DaveBerkeley/mains-power-control/kicad/mains-power-control/mains-power-control.kicad_sch

## KiCad design kicad/mains-power-control/mains-power-control.kicad_sch (2026-01-26)

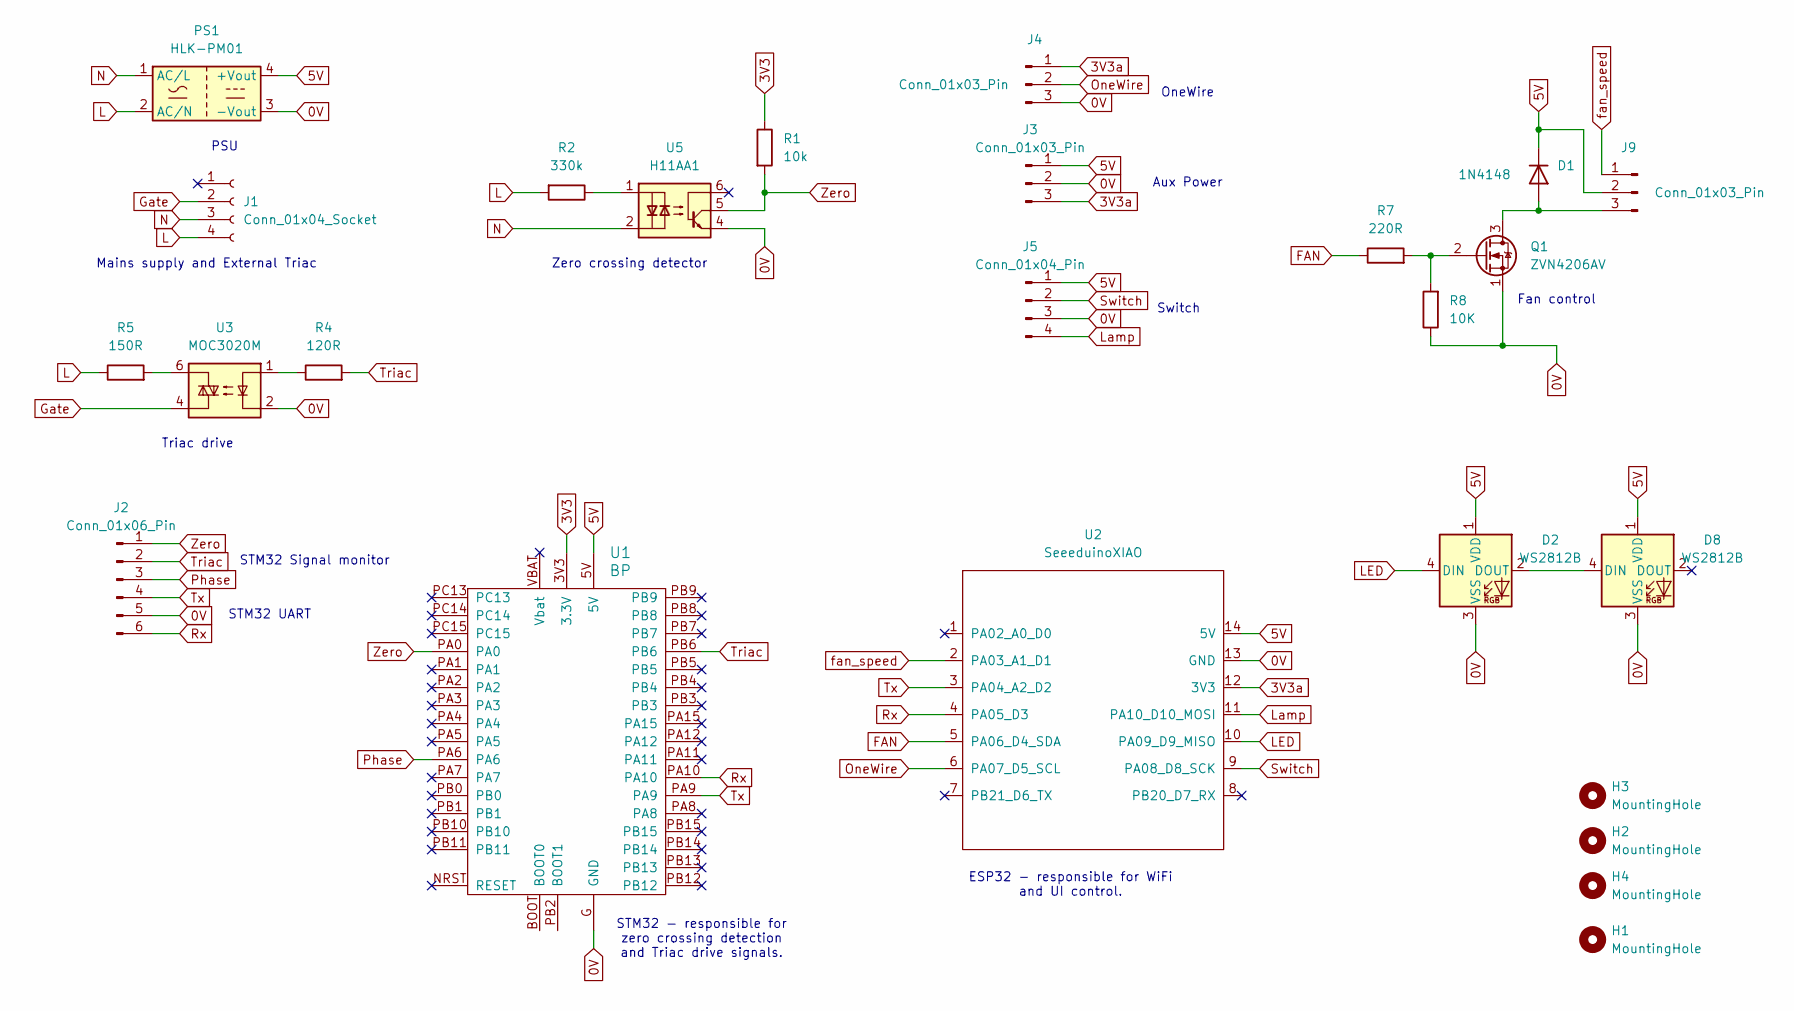
[picture p13: schematic mains-power-control.kicad_sch]

Parts:
D1: 1N4148; D_DO-41_SOD81_P7.62mm_Horizontal
D2, D8: WS2812B; LED_D8-YF923
H1, H2, H3, H4: MountingHole; MountingHole_3.2mm_M3
J1: Conn_01x04_Socket; PhoenixContact_MCV_1,5_4-G-5.08_1x04_P5.08mm_Vertical
J2: Conn_01x06_Pin; PinHeader_1x06_P2.54mm_Vertical
J3, J4, J9: Conn_01x03_Pin; PinHeader_1x03_P2.54mm_Vertical
J5: Conn_01x04_Pin; PinHeader_1x04_P2.54mm_Vertical
PS1: HLK-PM01; Converter_ACDC_Hi-Link_HLK-PMxx
Q1: ZVN4206AV; TO-92_Inline
R1: 10k; R_Axial_DIN0207_L6.3mm_D2.5mm_P7.62mm_Horizontal
R2: 330k; R_Axial_DIN0207_L6.3mm_D2.5mm_P7.62mm_Horizontal
R4: 120R; R_Axial_DIN0207_L6.3mm_D2.5mm_P7.62mm_Horizontal
R5: 150R; R_Axial_DIN0207_L6.3mm_D2.5mm_P7.62mm_Horizontal
R7: 220R; R_Axial_DIN0207_L6.3mm_D2.5mm_P7.62mm_Horizontal
R8: 10K; R_Axial_DIN0207_L6.3mm_D2.5mm_P7.62mm_Horizontal
U1: BP; blue_pill
U2: SeeeduinoXIAO; Seeeduino_XIAO-MOUDLE14P-2.54-21X17.8MM
U3: MOC3020M; DIP-6_W7.62mm
U5: H11AA1; DIP-6_W7.62mm

Connections:
0V: D2.3 (VSS), D8.3 (VSS), J2.5, J3.2, J4.3, J5.3, PS1.3 (-Vout), Q1.1 (S), R8.1, U1.G (GND), U2.13 (GND), U3.2, U5.4
3V3: R1.1, U1.3V3 (3.3V)
3V3a: J3.3, J4.1, U2.12 (3V3)
5V: D1.1 (K), D2.1 (VDD), D8.1 (VDD), J3.1, J5.1, J9.2, PS1.4 (+Vout), U1.5V, U2.14 (5V)
FAN: R7.1, U2.5 (PA06_D4_SDA)
Gate: J1.2, U3.4
L: J1.4, PS1.2 (AC/N), R2.2, R5.1
LED: D2.4 (DIN), U2.10 (PA09_D9_MISO)
Lamp: J5.4, U2.11 (PA10_D10_MOSI)
N: J1.3, PS1.1 (AC/L), U5.2
unnamed: D1.2 (A), J9.3, Q1.3 (D)
unnamed: D2.2 (DOUT), D8.4 (DIN)
unnamed: Q1.2 (G), R7.2, R8.2
unnamed: R2.1, U5.1
unnamed: R4.1, U3.1
unnamed: R5.2, U3.6
OneWire: J4.2, U2.6 (PA07_D5_SCL)
Phase: J2.3, U1.PA6
Rx: J2.6, U1.PA10, U2.4 (PA05_D3)
Switch: J5.2, U2.9 (PA08_D8_SCK)
Triac: J2.2, R4.2, U1.PB6
Tx: J2.4, U1.PA9, U2.3 (PA04_A2_D2)
Zero: J2.1, R1.2, U1.PA0, U5.5
fan_speed: J9.1, U2.2 (PA03_A1_D1)

Notes on the sheet:
OneWire
PSU
Triac drive
Switch
Zero crossing detector
ESP32 - responsible for WiFi and UI control.
STM32 UART
Aux Power
Mains supply and External Triac
Fan control
STM32 Signal monitor
STM32 - responsible for zero crossing detection and Triac drive signals.
