DaveBerkeley/mains-power-control/esp32/src/temperature.cpp

#include "panglos/debug.h"
#include "panglos/drivers/temperature.h"
#include "panglos/drivers/gpio.h"

#include "temperature.h"

TemperatureControl::TemperatureControl(TemperatureControlConfig *c)
:   config(*c),
    temperature(0),
    fan_state(false),
    valid(false)
{
    if (config.fan)
    {
        // if we have no temperature sensor, turn the fan on all the time
        config.fan->set(config.sensor ? false : true);
    }
    PO_DEBUG("fan_on=%d fan_off=%d alarm=%d", c->fan_on, c->fan_off, c->alarm);
}

void TemperatureControl::check_temperature()
{
    panglos::TemperatureSensor *sensor = config.sensor;
    if (!sensor) return;
    if (!sensor->ready()) return;

    double t;
    if (sensor->get_temp(& t))
    {
        valid = true;
        temperature = (int) t;
        fan_control();
    }
    sensor->start_conversion();
}

void TemperatureControl::set_fan(bool on)
{
    if (fan_state == on) return;
    fan_state = on;
    PO_DEBUG("fan %s t=%d", on ? "on" : "off", temperature);
    config.fan->set(on ^ config.fan_xor);
}

void TemperatureControl::fan_control()
{
    if (!config.fan) return;
    if (temperature < config.fan_off)
    {
        set_fan(false);
    }
    if (temperature > config.fan_on)
    {
        set_fan(true);
    }
}

void TemperatureControl::update()
{
    check_temperature();
}

bool TemperatureControl::alarm()
{
    return temperature >= config.alarm;
}

bool TemperatureControl::get_temperature(int *t)
{
    if (!valid) return false;
    if (t) *t = temperature;
    return true;
}

void TemperatureControl::set_sensor(panglos::TemperatureSensor *s)
{
    config.sensor = s;
}

//  FIN
