DaveBerkeley/mains-power-control/esp32/test/mains_control.cpp

#include <list>

#include <gtest/gtest.h>

#include "panglos/debug.h"
#include "panglos/object.h"
#include "panglos/time.h"

#include "panglos/drivers/gpio.h"
#include "panglos/drivers/uart.h"
#include "panglos/drivers/led_strip.h"
#include "panglos/drivers/temperature.h"

#include "panglos/app/event.h"

#include "mains_control.h"
#include "devices.h"

using namespace panglos;

namespace panglos {
    void ntp_start(Time::tick_t)
    {
        PO_DEBUG("");
    }
}

     /*
     *  Simulate a system populated with Devices
     */

class mc_SysSetup
{
public:
    mc_GPIO button;
    mc_GPIO fan;
    mc_LedStrip leds;
    mc_UART uart;
    mc_Temp temperature;

    mc_SysSetup()
    {
        // make sure it looks a bit like a recent boot
        Time::set(1);

        if (!Objects::objects)
        {
            Objects::objects = Objects::create();
        }

        Objects::objects->add("button", & button);
        Objects::objects->add("fan", & fan);
        Objects::objects->add("leds", & leds);
        Objects::objects->add("uart", & uart);
    }
    ~mc_SysSetup()
    {
        delete Objects::objects;
        Objects::objects = 0;
    }
};

    /*
     *
     */

TEST(MainsControl, Modes)
{
    mc_SysSetup sys;
    PowerControl *control = PowerControl::create(1000, -30);
    TemperatureControlConfig tc_config = {
        .fan = 0,
        .sensor = 0,
        .fan_on = 28,
        .fan_off = 25,
        .alarm = 40,
    };

    const PowerManager::Config config = {
        .pc = control,
        .leds = & sys.leds,
        .uart = & sys.uart,
        .button = & sys.button,
        .base = 20,
        .temp_control = & tc_config,
    };
    PowerManager *pm = PowerManager::create(& config);
    const uint8_t bright = 0x40;

    mc_LedStrip::LedState & state = sys.leds.state[0];

    // check modes

    // starts in ECO
    pm->on_idle();
    EXPECT_STREQ(pm->mode_name(pm->get_mode()), "eco");
    EXPECT_EQ(state.r, 0);
    EXPECT_EQ(state.g, bright);
    EXPECT_EQ(state.b, 0);

    pm->set_mode(PowerManager::M_OFF);
    pm->on_idle();
    EXPECT_STREQ(pm->mode_name(pm->get_mode()), "off");
    EXPECT_EQ(state.r, 0);
    EXPECT_EQ(state.g, 0);
    EXPECT_EQ(state.b, 0);

    pm->set_mode(PowerManager::M_ON);
    pm->on_idle();
    EXPECT_STREQ(pm->mode_name(pm->get_mode()), "on");
    EXPECT_EQ(state.r, bright);
    EXPECT_EQ(state.g, 0);
    EXPECT_EQ(state.b, 0);

    pm->set_mode(PowerManager::M_ECO);
    pm->on_idle();
    EXPECT_STREQ(pm->mode_name(pm->get_mode()), "eco");
    EXPECT_EQ(state.r, 0);
    EXPECT_EQ(state.g, bright);
    EXPECT_EQ(state.b, 0);

    pm->set_mode(PowerManager::M_BASE);
    pm->on_idle();
    EXPECT_STREQ(pm->mode_name(pm->get_mode()), "base");
    EXPECT_EQ(state.r, 0);
    EXPECT_EQ(state.g, 0);
    EXPECT_EQ(state.b, bright);

    delete pm;
    delete control;
}

TEST(MainsControl, Keys)
{
    mc_SysSetup sys;
    PowerControl *control = PowerControl::create(1000, -30);
    TemperatureControlConfig tc_config = {
        .fan = 0,
        .sensor = 0,
        .fan_on = 28,
        .fan_off = 25,
        .alarm = 40,
    };

    const PowerManager::Config config = {
        .pc = control,
        .leds = & sys.leds,
        .uart = & sys.uart,
        .button = & sys.button,
        .base = 20,
        .temp_control = & tc_config,
    };
    PowerManager *pm = PowerManager::create(& config);

    // check that the key presses cycle through the modes

    struct State
    {
        bool key;
        PowerManager::Mode mode;
    };

    static const struct State states[] = {
        {   true, PowerManager::M_ECO },
        {   true, PowerManager::M_ECO },
        {   false, PowerManager::M_BASE },
        {   true, PowerManager::M_BASE },
        {   true, PowerManager::M_BASE },
        {   true, PowerManager::M_BASE },
        {   false, PowerManager::M_OFF },
        {   false, PowerManager::M_OFF },
        {   false, PowerManager::M_OFF },
        {   false, PowerManager::M_OFF },
        {   true, PowerManager::M_OFF },
        {   true, PowerManager::M_OFF },
        {   false, PowerManager::M_ON },
        {   false, PowerManager::M_ON },
        {   false, PowerManager::M_ON },
        {   true, PowerManager::M_ON },
        {   true, PowerManager::M_ON },
        {   false, PowerManager::M_ECO },
        {   false, PowerManager::M_ECO },
        {   false, PowerManager::M_ECO },
        {   true, PowerManager::M_ECO },
    };

    //starts in ECO
    pm->on_idle();
    EXPECT_EQ(pm->get_mode(), PowerManager::M_ECO);

    for (const struct State &state : states)
    {
        sys.button.state = state.key;
        pm->on_tick();
        pm->on_idle();
        EXPECT_EQ(pm->get_mode(), state.mode);
    }

    delete pm;
    delete control;
}

TEST(MainsControl, Power)
{
    mc_SysSetup sys;
    PowerControl *control = PowerControl::create(1000, -30);
    TemperatureControlConfig tc_config = {
        .fan = 0,
        .sensor = 0,
        .fan_on = 28,
        .fan_off = 25,
        .alarm = 40,
    };

    const PowerManager::Config config = {
        .pc = control,
        .leds = & sys.leds,
        .uart = & sys.uart,
        .button = & sys.button,
        .base = 20,
        .temp_control = & tc_config,
    };
    PowerManager *pm = PowerManager::create(& config);

    // always full on
    pm->set_mode(PowerManager::M_ON);
    for (int p = -2000; p < 2000; p += 10)
    {
        pm->on_power(p);
        pm->on_idle();
        EXPECT_EQ(pm->get_percent(), 99);
    }

    // always off
    pm->set_mode(PowerManager::M_OFF);
    for (int p = -2000; p < 2000; p += 10)
    {
        pm->on_power(p);
        pm->on_idle();
        EXPECT_EQ(pm->get_percent(), 0);
    }

    // TODO : test for active modes

    delete pm;
    delete control;
}

    /*
     * P_net(t) = P_base_load(t) + α(t)·P_max - P_solar(t)
     *
     * P_base_load: uncontrollable loads (kettle, fridge, etc.) - disturbances
     * α(t): your control input, ∈ [0,1]
     * P_max: maximum load power (unknown parameter)
     * P_solar: disturbance (weather dependent)
     *
     */

#if 0

P_net(t) = P_base_load(t) + α(t)·P_max - P_solar(t)

#endif

class PowerSim
{
public:
    virtual ~PowerSim() { }

    virtual bool run() = 0;
    virtual int get_power() = 0;
    virtual int get_time() = 0;
};

    /*
     *
     */

struct Line
{
    int secs;
    int watts;
};

static void parse_line(char *line, struct Line *info)
{
    // "hh:mm:ss power"
    char *b = line;
    char *save = 0;
    const char *hh = strtok_r(b, ":", & save);
    const char *mm = strtok_r(0, ":", & save);
    const char *ss = strtok_r(0, " ", & save);
    const char *pp = strtok_r(0, "\n", & save);

    char *end = 0;
    int secs = 0;
    secs += (int) strtol(hh, & end, 10);
    secs *= 60;
    secs += (int) strtol(mm, & end, 10);
    secs *= 60;
    secs += (int) strtol(ss, & end, 10);
    int watts = (int) strtol(pp, & end, 10);

    info->secs = secs;
    info->watts = watts;
}

class RealData : public PowerSim
{
    int tick;
    FILE *file;
    int net;
public:
    RealData(const char *path)
    :   tick(0),
        file(0),
        net(0)
    {
        file = fopen(path, "r");
        ASSERT_ERROR(file, "path=%s", path);
    }
    ~RealData()
    {
        fclose(file);
    }

    virtual int get_time() override
    {
        return tick;
    }

    bool read()
    {
        tick += 1;

        char buff[128];
        char *s = fgets(buff, sizeof(buff), file);
        if (!s) return false;
        //PO_DEBUG("'%s'", s);

        struct Line info;
        parse_line(buff, & info);
        //PO_DEBUG("secs=%d net=%d", info.secs, info.solar);
        net = info.watts;
        
        return true;
    }

    virtual bool run() override
    {
        //return read();
        const int lo = 47483;
        const int hi = 50291;
        while (tick < lo)
        {
            if (!read())
                return false;
        }
        if (tick > hi)
            return false;

        return read();
    }

    virtual int get_power() override
    {
        return net;
    }
};

    /*
     *
     */

TEST(MainsControl, Solar)
{
    const int load = 1500;
    PowerControl *control = PowerControl::create(load, -30);

    RealData sim("test/solar3.log");
    int burn = 0;

    int total_burn = 0;
    int total_import = 0;
    int total_meter = 0;

    while (sim.run())
    {
        const int meter = sim.get_power();
        const int net = meter + burn;
        control->update(net);
        const int percent = control->get_percent();
        burn = load * percent / 100;
        //printf("xsim %d %d %d %d %d\n", sim.get_time(), meter, net, percent, burn);

        total_burn += burn;
        if (meter > 0)
            total_meter += meter;
        if (net > 0)
            total_import += net;
    }

    const int Wh = 60 * 60;
    total_meter /= Wh;
    total_burn /= Wh;
    total_import /= Wh;

    fprintf(stderr, "meter=%d burn=%d net=%d\n",
            total_meter, total_burn, total_import);
    int excess = total_import - total_meter;
    fprintf(stderr, "extra_imports=%d extra_free=%d \n", 
            excess,
            total_burn - excess
            );

    delete control;
}

    /*
     *
     */

TEST(MainsControl, Fan)
{
    mc_SysSetup sys;
    PowerControl *control = PowerControl::create(1000, -30);
    TemperatureControlConfig tc_config = {
        .fan = & sys.fan,
        .sensor = & sys.temperature,
        .fan_on = 28,
        .fan_off = 25,
        .alarm = 40,
    };

    const PowerManager::Config config = {
        .pc = control,
        .leds = & sys.leds,
        .uart = & sys.uart,
        .button = & sys.button,
        .base = 20,
        .temp_control = & tc_config,
    };
    PowerManager *pm = PowerManager::create(& config);

    sys.temperature.t = 10;
    for (int i = 1; i < 1000; i++)
    {
        if (i > 300) sys.temperature.t = 30;
        if (i > 500) sys.temperature.t = 20;
        if (i > 800) sys.temperature.t = 30;
        Time::set(i);
        pm->on_power(100);
        pm->on_idle();
        // valid on 100ms
        if ((Time::get() % 100) != 0) continue;

        if (i <= 300) { EXPECT_EQ(sys.fan.state, false); }
        else if (i <= 500) { EXPECT_EQ(sys.fan.state, true); }
        else if (i <= 800) { EXPECT_EQ(sys.fan.state, false); }
        else { EXPECT_EQ(sys.fan.state, true); }
    }
 
    delete pm;
    delete control;
}

    /*
     *
     */

TEST(MainsControl, Led)
{
    mc_SysSetup sys;
    PowerControl *control = PowerControl::create(1000, -30);
    TemperatureControlConfig tc_config = {
        .fan = 0,
        .sensor = 0,
        .fan_on = 28,
        .fan_off = 25,
        .alarm = 40,
    };

    const PowerManager::Config config = {
        .pc = control,
        .leds = & sys.leds,
        .uart = & sys.uart,
        .button = & sys.button,
        .base = 20,
        .temp_control = & tc_config,
    };
    PowerManager *pm = PowerManager::create(& config);

    pm->sim_led(true, 0, 1, 2, 3);
    pm->sim_led(true, 1, 3, 4, 5);

    EXPECT_EQ(sys.leds.state[0].r, 2);
    EXPECT_EQ(sys.leds.state[0].g, 1);
    EXPECT_EQ(sys.leds.state[0].b, 3);
    EXPECT_EQ(sys.leds.state[1].r, 4);
    EXPECT_EQ(sys.leds.state[1].g, 3);
    EXPECT_EQ(sys.leds.state[1].b, 5);

    delete pm;
    delete control;
}

//  FIN
